PM04290/LoRa2HA/enclosure/MLA30-top.stl

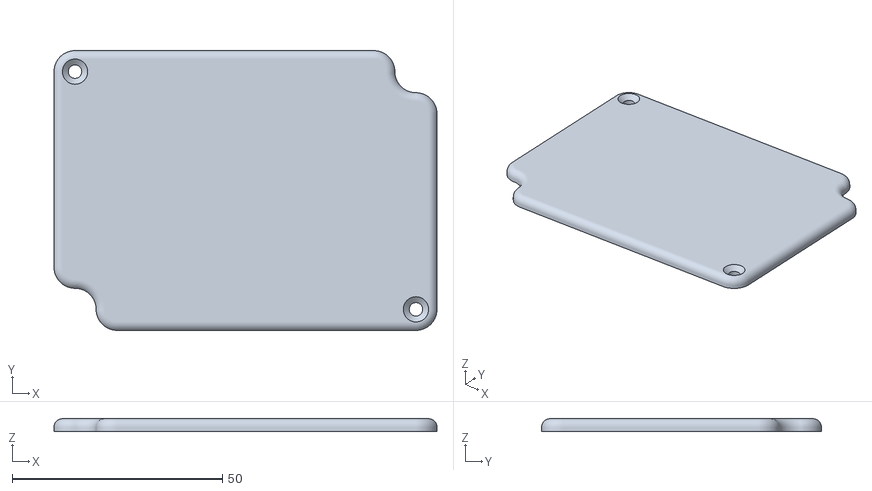
[picture p147: CAD file, 2024-12-08]
enclosure/MLA30-top.stl
91.0 x 66.5 x 3.00
