PM04290/LoRa2HA/enclosure/UPDI-top.stl

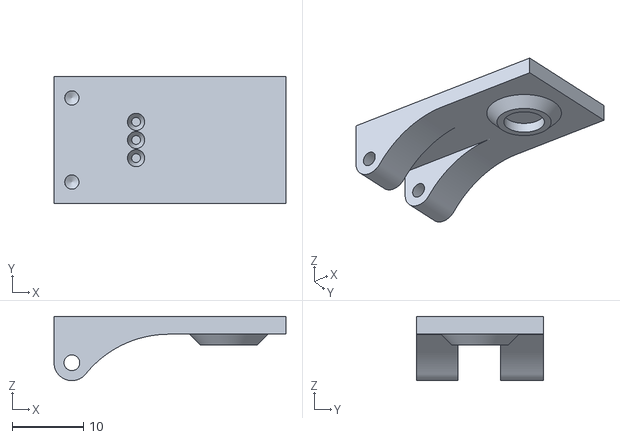
[picture p148: CAD file, 2024-12-08]
enclosure/UPDI-top.stl
32.5 x 17.8 x 9.00
