PM04290/LoRa2HA/HUBs/olds/lora2ha-HUB-V0-8/lora2ha-HUB-V0-8.ino

/*
  Designed for ESP32's series
  Radio module : SX1278 (Ra-01 / Ra-02)

  Wifi AP
    - default ssid : lora2ha
    - default password : 12345678
    - default address : 192.164.4.1 (lora2ha0.local)

  TODO
    Paramétrage distance
    Ajout (ou pas) de la carte LilyGO T-Internet POE ? ?

*/
#include <EEPROM.h>
#include <FS.h>
#include <SPIFFS.h>
#include "config.h"
#include <RadioLink.h>
#define ARDUINOJSON_ENABLE_NAN 1
#include <ArduinoJson.h>
#include <ESPAsyncWebServer.h>
#include "src/datetime.h"

#ifndef ESP32
#error Only designed for ESP32
#endif

//      PCB      MLH1          MLH2            MLH3         MLH4
// LoRa       Lolin ESP32   OLIMEX-POE      WT32-ETH01     ESP32
// pins        (S2 Mini)                                  MiniKit
// SCK             7            14              14           18
// MISO            9            15              15           19
// MOSI           11             2               2           23
// NSS             5             5              12            5
// NRST           12             4              4             4
// DIO0            3            36              35            2

RadioLinkClass RLcomm;

JsonDocument docJson;

// for rtc
DateTime rtc = DateTime(2020, 1, 1, 0, 0, 0);
volatile bool newRTC = false;
portMUX_TYPE ntpMux = portMUX_INITIALIZER_UNLOCKED;
// for availability
bool needPublishOnline = true;

typedef struct  __attribute__((packed))
{
  uint8_t version;
  int lqi;
  rl_packets packets;
} packet_version;

#define MAX_PACKET 20
packet_version packetTable[MAX_PACKET];
volatile byte idxReadTable = 0;
volatile byte idxWriteTable = 0;

bool eth_connected = false;

void MQTTcallback(char* topic, byte* payload, unsigned int length);

#include "devices.hpp"
#include "network.hpp"

// for 1 Second interrup
hw_timer_t* secTimer = NULL;
portMUX_TYPE timerMux = portMUX_INITIALIZER_UNLOCKED;
volatile bool topSecond = false;

// for NTP update
TaskHandle_t xHandleNTP = NULL;

// Callback for memory problem
void heap_caps_alloc_failed_hook(size_t requested_size, uint32_t caps, const char *function_name)
{
#ifdef DEBUG_SERIAL
  printf("!!! %s failed to allocate %d bytes with 0x%X capabilities. \n", function_name, requested_size, caps);
  printf("heap_caps_get_largest_free_block: %d\n", heap_caps_get_largest_free_block(MALLOC_CAP_8BIT));
#endif
}

void IRAM_ATTR onTimer()
{
  portENTER_CRITICAL_ISR(&timerMux);
  topSecond = true;
  portEXIT_CRITICAL_ISR(&timerMux);
}

#define RETRY_NTP 10
void TaskNTP(void *pvParameters)
{
  DateTime* _rtc = (DateTime*)pvParameters;
  const TickType_t xDelay = 2000 / portTICK_PERIOD_MS;
  configTzTime(datetimeTZ, datetimeNTP, defaultNTP);
  while (true)
  {
    struct tm timeinfo;
    uint8_t retry = RETRY_NTP;
    while (retry > 0) {
      if (getLocalTime(&timeinfo))
      {
        timeinfo.tm_year += 1900;
        timeinfo.tm_mon += 1;
        DEBUGf("NTP:%04d-%02d-%02d %02d:%02d:%02d\n", timeinfo.tm_year, timeinfo.tm_mon, timeinfo.tm_mday, timeinfo.tm_hour, timeinfo.tm_min, timeinfo.tm_sec);
        portENTER_CRITICAL_ISR(&ntpMux);
        *_rtc = DateTime(timeinfo.tm_year, timeinfo.tm_mon, timeinfo.tm_mday, timeinfo.tm_hour, timeinfo.tm_min, timeinfo.tm_sec);
        newRTC = true;
        portEXIT_CRITICAL_ISR(&ntpMux);
        retry = 0;
      } else {
        retry--;
        DEBUGf("NTP:no time yet %d/10\n", RETRY_NTP - retry);
        vTaskDelay( xDelay );
      }
    }
    vTaskSuspend( NULL );
  }
}

bool getPacket(packet_version* p)
{
  if (idxReadTable != idxWriteTable)
  {
    *p = packetTable[idxReadTable];
    //
    idxReadTable++;
    if (idxReadTable >= MAX_PACKET)
    {
      idxReadTable = 0;
    }
    return true;
  }
  return false;
}

void onLoRaReceive(uint8_t len, rl_packet_t* p)
{
  noInterrupts();
  memcpy(&packetTable[idxWriteTable].packets.current, p, len);
  packetTable[idxWriteTable].version = 1;
  packetTable[idxWriteTable].lqi = RLcomm.lqi();
  if (len == RL_PACKETV1_SIZE) packetTable[idxWriteTable].version = 1;
  idxWriteTable++;
  if (idxWriteTable >= MAX_PACKET)
  {
    idxWriteTable = 0;
  }
  if (idxWriteTable == idxReadTable) // overload
  {
    idxReadTable++;
    if (idxReadTable >= MAX_PACKET)
    {
      idxReadTable = 0;
    }
  }
  interrupts();
}

void processLoRa()
{
  packet_version p;
  if (getPacket(&p))
  {
    rl_packet_t* cp = &p.packets.current;
    DEBUGf("V%d[%d%%] %d <= %d:%d = %d\n", p.version, p.lqi, cp->destinationID, cp->senderID, cp->childID, cp->data.num.value);

    if (logPacket)
    {
      notifyLogPacket(cp, p.lqi);
    }

    if (cp->destinationID == UIDcode) // Only for me
    {
      if (cp->senderID == RL_ID_PING) // if senderID = 254, ping needed
      {
        RLcomm.publishNum(RL_ID_PING, UIDcode, RL_ID_PING, p.lqi);
        return;
      }
      if (cp->childID == RL_ID_DATETIME) // from every sender, if ChildID = 0xFC (DATETIME), sender need Datetime
      {
        hub.processDateTime(cp->senderID);
      }
      Device* dev = hub.getDeviceById(cp->senderID);
      Child* ch = hub.getChildById(cp->senderID, cp->childID);
      if (ch != nullptr)
      {
        // process existing device
        switch (p.version) {
          case 1:
            ch->doPacketForHA(*cp);
            break;
          default:
            ch->doPacketForHA(*cp);
            break;
        }
        if (dev) {
          dev->setLQI(p.lqi);
        }
      } else {
        if (cp->childID == RL_ID_CONFIG && (rl_element_t)(cp->sensordataType >> 3) == E_CONFIG)
        { // config packet
          int d;
          int c;
          String js;
          dev = hub.getDeviceById(cp->senderID);
          rl_conf_t cnfIdx = (rl_conf_t)(cp->sensordataType & 0x07);
          if (cnfIdx == C_BASE)
          { // Basic configuration
            rl_configBase_t* cnfb = (rl_configBase_t*)&cp->data.configs.base;
            rl_element_t st = (rl_element_t)cnfb->deviceType;
            rl_data_t dt = (rl_data_t)cnfb->dataType;
            DEBUGf("Conf B %d %d %s %d %d\n", cp->senderID, cnfb->childID, cnfb->name, (int)st, (int)dt);
            if (dev == nullptr)
            {
              d = hub.getNbDevice(); // before adding (1st is 0)
              if (cnfb->childID == RL_ID_CONFIG) {
                dev = hub.addDevice(new Device(cp->senderID, cnfb->name, false));
              } else {
                dev = hub.addDevice(new Device(cp->senderID, "", false));
              }
              if (!dev) {
                DEBUGf("** Error adding new device %d\n", cp->senderID);
                return;
              }
            }
            if (cnfb->childID != RL_ID_CONFIG)
            {
              d = hub.getIdxDeviceByAddress(cp->senderID);
              ch = dev->getChildById(cnfb->childID);
              if (ch == nullptr)
              {
                c = dev->getNbChild(); // before adding (1st is 0)
                char cName[sizeof(cnfb->name) + 1];
                strncpy(cName, cnfb->name, sizeof(cnfb->name));
                cName[sizeof(cnfb->name)] = 0;
                ch = new Child(dev, cnfb->childID, cName, st, dt, "", CategoryAuto, "");
                if (!ch) {
                  DEBUGf("Error adding new chid %d on device %d\n", cnfb->childID, cp->senderID);
                  return;
                }
                ch = dev->addChild(ch);
              }
            }
          } else {
            ch = dev->getChildById(cp->data.configs.base.childID);
          }
          DEBUG((long)dev); DEBUG(" "); DEBUGln((long)ch);
          if (cnfIdx == C_UNIT && dev && ch) {
            rl_configText_t* cnft = (rl_configText_t*)&cp->data.configs.text;
            uint8_t childID = cnft->childID;
            char txt[sizeof(cnft->text) + 1];
            strncpy(txt, cnft->text, sizeof(cnft->text));
            txt[sizeof(cnft->text)] = 0;
            DEBUGf("Conf U %d %s\n", childID, txt);
            if (ch) {
              ch->setUnit(txt);
            }
          }
          if (cnfIdx == C_OPTS && dev) {
            rl_configText_t* cnft = (rl_configText_t*)&cp->data.configs.text;
            uint8_t childID = cnft->childID;
            char txt[sizeof(cnft->text) + 1];
            strncpy(txt, cnft->text, sizeof(cnft->text));
            txt[sizeof(cnft->text)] = 0;
            DEBUGf("Conf O %d %s\n", childID, txt);
            if (childID == RL_ID_CONFIG) {
              if (dev) {
                dev->setModel(txt);
              }
            } else {
              if (ch) {
                ch->setSelectOptions(txt);
              }
            }
          }
          if (cnfIdx == C_NUMS && dev && ch) {
            rl_configNums_t* cnfn = (rl_configNums_t*)&cp->data.configs.nums;
            uint8_t childID = cnfn->childID;
            DEBUGf("Conf N %d %d %d %d\n", childID, cnfn->divider, cnfn->mini, cnfn->maxi);
            if (ch) {
              if (cnfn->divider == 0) cnfn->divider = 1;
              ch->setNumberConfig(cnfn->mini, cnfn->maxi, cnfn->divider);
            }
          }
          if (cnfIdx == C_END && dev) {
            d = hub.getIdxDeviceByAddress(cp->senderID);
            DEBUGf("Conf END %d %d\n", d, c);
            if (cp->data.configs.base.childID == RL_ID_CONFIG)
            {
              // add device
              docJson.clear();
              docJson["cmd"] = "devnotify";
              docJson["conf_child_" + String(d) + "_"] = getHTMLforDevice(d, dev);
              js = "";
              serializeJson(docJson, js);
              DEBUGln(js);
              ws.textAll(js);
            } else {
              c = dev->getIdxChildById(cp->data.configs.base.childID);
              // add child
              docJson.clear();
              docJson["cmd"] = "childnotify";
              docJson["conf_child_" + String(d) + "_" + String(c)] = getHTMLforChild(d, c, ch);
              js = "";
              serializeJson(docJson, js);
              ws.textAll(js);
            }
          }
        }
      }
    }
  }
}

void MQTTcallback(char* topic, byte* payload, unsigned int length)
{
  char p[length + 1];
  strncpy(p, (char*)payload, length);
  p[length] = 0;
  hub.onMessageMQTT(topic, p);
}

void setup()
{
#ifdef DEBUG_SERIAL
  Serial.begin(115200);
  while (!Serial.availableForWrite()) delay(10);
#endif
  esp_err_t error = heap_caps_register_failed_alloc_callback(heap_caps_alloc_failed_hook);
  DEBUGln("Start debug");

  if (!SPIFFS.begin())
  {
    DEBUGln(F("SPIFFS Mount failed"));
  } else
  {
    DEBUGln(F("SPIFFS Mount succesfull"));
    listDir("/");
  }
  delay(50);

  if (!EEPROM.begin(EEPROM_MAX_SIZE))
  {
    DEBUGln("failed to initialise EEPROM");
  } else {
    /* to initialize EEPROM with config.h defines
          EEPROM.writeChar(0, AP_ssid[7]);
          EEPROM.writeString(EEPROM_TEXT_OFFSET, Wifi_ssid);
          EEPROM.writeString(EEPROM_TEXT_OFFSET + (EEPROM_TEXT_SIZE * 1), Wifi_pass);
          EEPROM.writeString(EEPROM_TEXT_OFFSET + (EEPROM_TEXT_SIZE * 2), mqtt_host);
          EEPROM.writeString(EEPROM_TEXT_OFFSET + (EEPROM_TEXT_SIZE * 3), mqtt_user);
          EEPROM.writeString(EEPROM_TEXT_OFFSET + (EEPROM_TEXT_SIZE * 4), mqtt_pass);
          EEPROM.writeString(EEPROM_TEXT_OFFSET + (EEPROM_TEXT_SIZE * 5), datetimeTZ);
          EEPROM.writeString(EEPROM_TEXT_OFFSET + (EEPROM_TEXT_SIZE * 6), datetimeNTP);
          EEPROM.commit();
    */
    char code = EEPROM.readChar(EEPROM_DATA_CODE);
    if (code >= '0' && code <= '9')
    {
      UIDcode = code - '0';
      AP_ssid[strlen(AP_ssid) - 1] = code;
      RadioFreq = EEPROM.readUShort(EEPROM_DATA_FREQ);
      if (RadioFreq == 0xFFFF) RadioFreq = 433;
      Watchdog = EEPROM.readByte(EEPROM_DATA_WDOG) % 60;
      strcpy(Wifi_ssid, EEPROM.readString(EEPROM_TEXT_OFFSET).c_str());
      strcpy(Wifi_pass, EEPROM.readString(EEPROM_TEXT_OFFSET + EEPROM_TEXT_SIZE * 1).c_str());
      strcpy(mqtt_host, EEPROM.readString(EEPROM_TEXT_OFFSET + EEPROM_TEXT_SIZE * 2).c_str());
      strcpy(mqtt_user, EEPROM.readString(EEPROM_TEXT_OFFSET + EEPROM_TEXT_SIZE * 3).c_str());
      strcpy(mqtt_pass, EEPROM.readString(EEPROM_TEXT_OFFSET + EEPROM_TEXT_SIZE * 4).c_str());
      strcpy(datetimeTZ, EEPROM.readString(EEPROM_TEXT_OFFSET + EEPROM_TEXT_SIZE * 5).c_str());
      strcpy(datetimeNTP, EEPROM.readString(EEPROM_TEXT_OFFSET + EEPROM_TEXT_SIZE * 6).c_str());

      DEBUGln(AP_ssid);
      DEBUGf("Freq:%d\n", RadioFreq);
      DEBUGf("Wd:%d\n", Watchdog);
      DEBUGln(Wifi_ssid);
      DEBUGln(Wifi_pass);
      DEBUGln(mqtt_host);
      DEBUGln(mqtt_user);
      DEBUGln(mqtt_pass);
      DEBUGln(datetimeTZ);
      DEBUGln(datetimeNTP);
    }
  }

  // distance 3 = 1484 ms
  //          2 = 660 ms
  //          1 = 186 ms
  //          0 = 27 ms
  RadioDist = 1;
  if (RLcomm.begin(RadioFreq * 1E6, onLoRaReceive, NULL, 20, RadioDist))
  {
    RLcomm.setWaitOnTx(true);
    DEBUGf("LoRa ok at %dMHz (dist:%d)\n", RadioFreq, RadioDist);
  } else {
    DEBUGln("LoRa ERROR");
  }

  initNetwork();
  initWeb();

  if (loadConfig())
  {
    byte mac[6];
    WiFi.macAddress(mac);
    // HA
    hub.setUniqueId(mac, sizeof(mac));
  }
  // define time ISR
  secTimer = timerBegin(0, 80, true);
  timerAttachInterrupt(secTimer, &onTimer, true);
  timerAlarmWrite(secTimer, 1000000, true);
  timerAlarmEnable(secTimer);
  //
  DEBUGf("heap_caps_get_largest_free_block: %d\n", heap_caps_get_largest_free_block(MALLOC_CAP_8BIT));

  xTaskCreate( TaskNTP, "getNTP", 2048, (void*)&rtc, tskIDLE_PRIORITY, &xHandleNTP );
}

void loop()
{
  static uint32_t ntick = 0;
  bool doWatchDog = false;
  bool do24Hour = false;
  if (topSecond)
  {
    portENTER_CRITICAL(&timerMux);
    topSecond = false;
    portEXIT_CRITICAL(&timerMux);
    //
    uint32_t t = rtc.unixtime() + 1;
    portENTER_CRITICAL_ISR(&ntpMux);
    rtc = t;
    portEXIT_CRITICAL_ISR(&ntpMux);
    //DEBUGf("%02d:%02d:%02d\n", rtc.hour(), rtc.minute(), rtc.second());
    //
    ntick++;
    doWatchDog = ((ntick % (DEFAULT_ONLINE_WATCHDOG * 60)) == 0);
    if (ntick >= 86400) { // 1 day
      ntick = 0;
      do24Hour = true;
    }
  }
  if (doWatchDog) {
    // must publish "Online" every 10 minutes
    DEBUGln("Need publish Online");
    needPublishOnline = true;
  }
  if (do24Hour) {
    // get NTP time every days (re-activate Task)
    vTaskResume( xHandleNTP );
  }
  if (newRTC) {
    // when NTP updated, process it
    hub.processDateTime(RL_ID_BROADCAST);
    portENTER_CRITICAL_ISR(&ntpMux);
    newRTC = false;
    portEXIT_CRITICAL_ISR(&ntpMux);
  }
  processLoRa();
  hub.processMQTT();
}

bool loadConfig()
{
  DEBUGln("Loading config file");
  File file = SPIFFS.open("/config.json");
  if (!file || file.isDirectory())
  {
    DEBUGln("failed to open config file");
    return false;
  }
  Device* dev;

  DeserializationError error = deserializeJson(docJson, file);
  file.close();
  if (error)
  {
    DEBUGln("failed to deserialize config file");
    return false;
  }

  // walk device array
  JsonVariant devices = docJson["dev"];
  if (devices.is<JsonArray>())
  {
    for (JsonVariant deviceItem : devices.as<JsonArray>())
    {
      if (!deviceItem.isNull())
      {
        uint8_t address = deviceItem["address"].as<int>();
        const char* name = deviceItem["name"].as<const char*>();
        uint8_t rlversion = deviceItem["rlversion"].as<int>();
        DEBUGf("@ %d : %s\n", address, name);
        if ((address > 0) && (dev = hub.addDevice(new Device(address, name, true, rlversion))))
        {
          if (deviceItem["model"].is<const char*>()) {
            dev->setModel(deviceItem["model"].as<const char*>());
          }
          // walk child array
          JsonVariant childs = deviceItem["childs"];
          if (childs.is<JsonArray>())
          {
            for (JsonVariant childItem : childs.as<JsonArray>())
            {
              uint8_t childID = childItem["id"];
              const char* lbl = childItem["label"].as<const char*>();
              rl_element_t st = (rl_element_t)childItem["sensortype"].as<int>();
              rl_data_t dt = (rl_data_t)childItem["datatype"].as<int>();
              int expire = childItem["expire"] | 0L;
              int32_t mini(LONG_MIN);
              if (childItem["min"].is<int>())
                mini = childItem["min"].as<int>();
              int32_t maxi(LONG_MAX);
              if (childItem["max"].is<int>())
                maxi = childItem["max"].as<int>();
              float coefA = 1.;
              if (childItem["coefa"].is<float>())
                coefA = childItem["coefa"];
              float coefB = 0.;
              if (childItem["coefb"].is<float>())
                coefB = childItem["coefb"];
              EntityCategory ec = EntityCategory::CategoryAuto;
              if (childItem["category"].is<int>()) {
                ec = (EntityCategory)childItem["category"].as<int>();
              }
              if (st == E_SELECT || st == E_INPUTNUMBER) {
                ec = EntityCategory::CategoryConfig;
              }
              Child* ch = dev->addChild(new Child(dev, childID, lbl, st, dt, childItem["class"].as<const char*>(), ec, childItem["unit"].as<const char*>(), expire, mini, maxi, coefA, coefB));
              if (st == E_SELECT)
              {
                ch->setSelectOptions(childItem["options"].as<const char*>());
              }
              if (st == E_INPUTNUMBER)
              {
                ch->setNumberConfig(childItem["imin"].as<int>(), childItem["imax"].as<int>(), childItem["idiv"].as<int>());
              }
            }
          }
        }
      }
    }
  }
  docJson.clear();
  DEBUGln("Config file loaded");
  return true;
}
