PM04290/LoRa2HA/HUBs/lora2ha-HUB-V1-4/src/datetime.cpp

// based on RTClib

#include "datetime.h"

#define DS3231_ADDRESS 0x68   ///< I2C address for DS3231


const uint8_t daysInMonth[] PROGMEM = {31, 28, 31, 30, 31, 30, 31, 31, 30, 31, 30};

/**************************************************************************/
/*!
    @brief  Given a date, return number of days since 2000/01/01,
            valid for 2000--2099
    @param y Year
    @param m Month
    @param d Day
    @return Number of days
*/
/**************************************************************************/
static uint16_t date2days(uint16_t y, uint8_t m, uint8_t d) {
  if (y >= 2000U)
    y -= 2000U;
  uint16_t days = d;
  for (uint8_t i = 1; i < m; ++i) {
    days += pgm_read_byte(daysInMonth + i - 1);
  }
  if (m > 2 && y % 4 == 0)
    ++days;
  return days + (365 * y) + ((y + 3) / 4) - 1;
}

/**************************************************************************/
/*!
    @brief  Given a number of days, hours, minutes, and seconds, return the
   total seconds
    @param days Days
    @param h Hours
    @param m Minutes
    @param s Seconds
    @return Number of seconds total
*/
/**************************************************************************/
static uint32_t time2ulong(uint16_t days, uint8_t h, uint8_t m, uint8_t s) {
  return ((days * 24UL + h) * 60 + m) * 60 + s;
}

static uint8_t bcd2bin(uint8_t val) {
  return val - 6 * (val >> 4);
}
static uint8_t bin2bcd(uint8_t val) {
  return val + 6 * (val / 10);
}

/**************************************************************************/
/*!
    @brief  Constructor from
        [Unix time](https://en.wikipedia.org/wiki/Unix_time).

    This builds a DateTime from an integer specifying the number of seconds
    elapsed since the epoch: 1970-01-01 00:00:00. This number is analogous
    to Unix time, with two small differences:

     - The Unix epoch is specified to be at 00:00:00
       [UTC](https://en.wikipedia.org/wiki/Coordinated_Universal_Time),
       whereas this class has no notion of time zones. The epoch used in
       this class is then at 00:00:00 on whatever time zone the user chooses
       to use, ignoring changes in DST.

     - Unix time is conventionally represented with signed numbers, whereas
       this constructor takes an unsigned argument. Because of this, it does
       _not_ suffer from the
       [year 2038 problem](https://en.wikipedia.org/wiki/Year_2038_problem).

    If called without argument, it returns the earliest time representable
    by this class: 2000-01-01 00:00:00.

    @see The `unixtime()` method is the converse of this constructor.

    @param t Time elapsed in seconds since 1970-01-01 00:00:00.
*/
/**************************************************************************/
DateTime::DateTime(uint32_t t) {
  t -= SECONDS_FROM_1970_TO_2000; // bring to 2000 timestamp from 1970

  ss = t % 60;
  t /= 60;
  mm = t % 60;
  t /= 60;
  hh = t % 24;
  uint16_t days = t / 24;
  uint8_t leap;
  for (yOff = 0;; ++yOff) {
    leap = yOff % 4 == 0;
    if (days < 365U + leap)
      break;
    days -= 365 + leap;
  }
  for (m = 1; m < 12; ++m) {
    uint8_t daysPerMonth = pgm_read_byte(daysInMonth + m - 1);
    if (leap && m == 2)
      ++daysPerMonth;
    if (days < daysPerMonth)
      break;
    days -= daysPerMonth;
  }
  d = days + 1;
}

/**************************************************************************/
/*!
    @brief  Constructor from (year, month, day, hour, minute, second).
    @warning If the provided parameters are not valid (e.g. 31 February),
           the constructed DateTime will be invalid.
    @see   The `isValid()` method can be used to test whether the
           constructed DateTime is valid.
    @param year Either the full year (range: 2000--2099) or the offset from
        year 2000 (range: 0--99).
    @param month Month number (1--12).
    @param day Day of the month (1--31).
    @param hour,min,sec Hour (0--23), minute (0--59) and second (0--59).
*/
/**************************************************************************/
DateTime::DateTime(uint16_t year, uint8_t month, uint8_t day, uint8_t hour, uint8_t min, uint8_t sec) {
  if (year >= 2000U)
    year -= 2000U;
  yOff = year;
  m = month;
  d = day;
  hh = hour;
  mm = min;
  ss = sec;
}

/**************************************************************************/
/*!
    @brief  Copy constructor.
    @param copy DateTime to copy.
*/
/**************************************************************************/
DateTime::DateTime(const DateTime &copy) : yOff(copy.yOff), m(copy.m), d(copy.d), hh(copy.hh), mm(copy.mm), ss(copy.ss) {}

/**************************************************************************/
/*!
    @brief  Convert a string containing two digits to uint8_t, e.g. "09" returns
   9
    @param p Pointer to a string containing two digits
*/
/**************************************************************************/
static uint8_t conv2d(const char *p) {
  uint8_t v = 0;
  if ('0' <= *p && *p <= '9')
    v = *p - '0';
  return 10 * v + *++p - '0';
}


/**************************************************************************/
/*!
    @brief  Constructor for creating a DateTime from an ISO8601 date string.

    This constructor expects its parameters to be a string in the
    https://en.wikipedia.org/wiki/ISO_8601 format, e.g:

    "2020-06-25T15:29:37"

    Usage:

    ```
    DateTime dt("2020-06-25T15:29:37");
    ```

    @note The year must be > 2000, as only the yOff is considered.

    @param iso8601dateTime
           A dateTime string in iso8601 format,
           e.g. "2020-06-25T15:29:37".

*/
/**************************************************************************/
DateTime::DateTime(const char *iso8601dateTime) {
  char ref[] = "2000-01-01T00:00:00";
  memcpy(ref, iso8601dateTime, min(strlen(ref), strlen(iso8601dateTime)));
  yOff = conv2d(ref + 2);
  m = conv2d(ref + 5);
  d = conv2d(ref + 8);
  hh = conv2d(ref + 11);
  mm = conv2d(ref + 14);
  ss = conv2d(ref + 17);
}

/**************************************************************************/
/*!
    @brief  Check whether this DateTime is valid.
    @return true if valid, false if not.
*/
/**************************************************************************/
bool DateTime::isValid() const {
  if (yOff >= 100)
    return false;
  DateTime other(unixtime());
  return yOff == other.yOff && m == other.m && d == other.d && hh == other.hh && mm == other.mm && ss == other.ss;
}

/**************************************************************************/
/*!
    @brief  Return the day of the week.
    @return Day of week as an integer from 0 (Sunday) to 6 (Saturday).
*/
/**************************************************************************/
uint8_t DateTime::dayOfTheWeek() const {
  uint16_t day = date2days(yOff, m, d);
  return (day + 6) % 7; // Jan 1, 2000 is a Saturday, i.e. returns 6
}

/**************************************************************************/
/*!
    @brief  Return Unix time: seconds since 1 Jan 1970.

    @see The `DateTime::DateTime(uint32_t)` constructor is the converse of
        this method.

    @return Number of seconds since 1970-01-01 00:00:00.
*/
/**************************************************************************/
uint32_t DateTime::unixtime(void) const {
  uint32_t t;
  uint16_t days = date2days(yOff, m, d);
  t = time2ulong(days, hh, mm, ss);
  t += SECONDS_FROM_1970_TO_2000; // seconds from 1970 to 2000
  return t;
}

/**************************************************************************/
/*!
    @brief  Convert the DateTime to seconds since 1 Jan 2000

    The result can be converted back to a DateTime with:

    ```cpp
    DateTime(SECONDS_FROM_1970_TO_2000 + value)
    ```

    @return Number of seconds since 2000-01-01 00:00:00.
*/
/**************************************************************************/
uint32_t DateTime::secondstime(void) const {
  uint32_t t;
  uint16_t days = date2days(yOff, m, d);
  t = time2ulong(days, hh, mm, ss);
  return t;
}

/**************************************************************************/
/*!
    @brief  Add a TimeSpan to the DateTime object
    @param span TimeSpan object
    @return New DateTime object with span added to it.
*/
/**************************************************************************/
DateTime DateTime::operator+(const TimeSpan &span) const {
  return DateTime(unixtime() + span.totalseconds());
}

/**************************************************************************/
/*!
    @brief  Subtract a TimeSpan from the DateTime object
    @param span TimeSpan object
    @return New DateTime object with span subtracted from it.
*/
/**************************************************************************/
DateTime DateTime::operator-(const TimeSpan &span) const {
  return DateTime(unixtime() - span.totalseconds());
}

/**************************************************************************/
/*!
    @brief  Subtract one DateTime from another

    @note Since a TimeSpan cannot be negative, the subtracted DateTime
        should be less (earlier) than or equal to the one it is
        subtracted from.

    @param right The DateTime object to subtract from self (the left object)
    @return TimeSpan of the difference between DateTimes.
*/
/**************************************************************************/
TimeSpan DateTime::operator-(const DateTime &right) const {
  return TimeSpan(unixtime() - right.unixtime());
}

/**************************************************************************/
/*!
    @author Anton Rieutskyi
    @brief  Test if one DateTime is less (earlier) than another.
    @warning if one or both DateTime objects are invalid, returned value is
        meaningless
    @see use `isValid()` method to check if DateTime object is valid
    @param right Comparison DateTime object
    @return True if the left DateTime is earlier than the right one,
        false otherwise.
*/
/**************************************************************************/
bool DateTime::operator<(const DateTime &right) const {
  return (yOff + 2000U < right.year() ||
         (yOff + 2000U == right.year() && (m < right.month() ||
		                                  (m == right.month() && (d < right.day() ||
										                         (d == right.day() && (hh < right.hour() ||
                                                                                      (hh == right.hour() && (mm < right.minute() ||
                                                                                                             (mm == right.minute() && ss < right.second()))))))))));
}

/**************************************************************************/
/*!
    @author Anton Rieutskyi
    @brief  Test if two DateTime objects are equal.
    @warning if one or both DateTime objects are invalid, returned value is
        meaningless
    @see use `isValid()` method to check if DateTime object is valid
    @param right Comparison DateTime object
    @return True if both DateTime objects are the same, false otherwise.
*/
/**************************************************************************/
bool DateTime::operator==(const DateTime &right) const {
  return (right.year() == yOff + 2000U && right.month() == m &&
          right.day() == d && right.hour() == hh && right.minute() == mm &&
          right.second() == ss);
}

/**************************************************************************/
/*!
    @brief  Return a ISO 8601 timestamp as a `String` object.

    The generated timestamp conforms to one of the predefined, ISO
    8601-compatible formats for representing the date (if _opt_ is
    `TIMESTAMP_DATE`), the time (`TIMESTAMP_TIME`), or both
    (`TIMESTAMP_FULL`).

    @see The `toString()` method provides more general string formatting.

    @param opt Format of the timestamp
    @return Timestamp string, e.g. "2020-04-16T18:34:56".
*/
/**************************************************************************/
String DateTime::timestamp(timestampOpt opt) const {
  char buffer[25]; // large enough for any DateTime, including invalid ones

  // Generate timestamp according to opt
  switch (opt) {
  case TIMESTAMP_TIME:
    // Only time
    sprintf(buffer, "%02d:%02d:%02d", hh, mm, ss);
    break;
  case TIMESTAMP_DATE:
    // Only date
    sprintf(buffer, "%u-%02d-%02d", 2000U + yOff, m, d);
    break;
  default:
    // Full
    sprintf(buffer, "%u-%02d-%02dT%02d:%02d:%02d", 2000U + yOff, m, d, hh, mm,
            ss);
  }
  return String(buffer);
}

bool DateTime::readDS3231() {
  Wire.beginTransmission(DS3231_ADDRESS);
  Wire.write(byte(0x00));
  if (Wire.endTransmission() == 0)
  {
    if (Wire.requestFrom(DS3231_ADDRESS, 7) == 7)
    {
      ss = bcd2bin(Wire.read() & 0x7F);
      mm = bcd2bin(Wire.read());
      hh = bcd2bin(Wire.read());
	  uint8_t scrap = Wire.read();
      d = bcd2bin(Wire.read());
      m = bcd2bin(Wire.read() & 0x7F);
      yOff = bcd2bin(Wire.read());
      return true;
    }
  }
  return false;
}

bool DateTime::writeDS3231() {
	Wire.beginTransmission(DS3231_ADDRESS);
	Wire.write(0); // set next input to start at the seconds register
	Wire.write(bin2bcd(ss)); // set seconds
	Wire.write(bin2bcd(mm)); // set minutes
	Wire.write(bin2bcd(hh)); // set hours
	Wire.write(bin2bcd(dayOfTheWeek() + 1)); // set day of week (1=Sunday, 7=Saturday)
	Wire.write(bin2bcd(d)); // set date (1 to 31)
	Wire.write(bin2bcd(m)); // set month
	Wire.write(bin2bcd(yOff)); // set year (0 to 99)
	return Wire.endTransmission();
}
